RBSC/BSA/Engraving/bsa_engraving.bmp

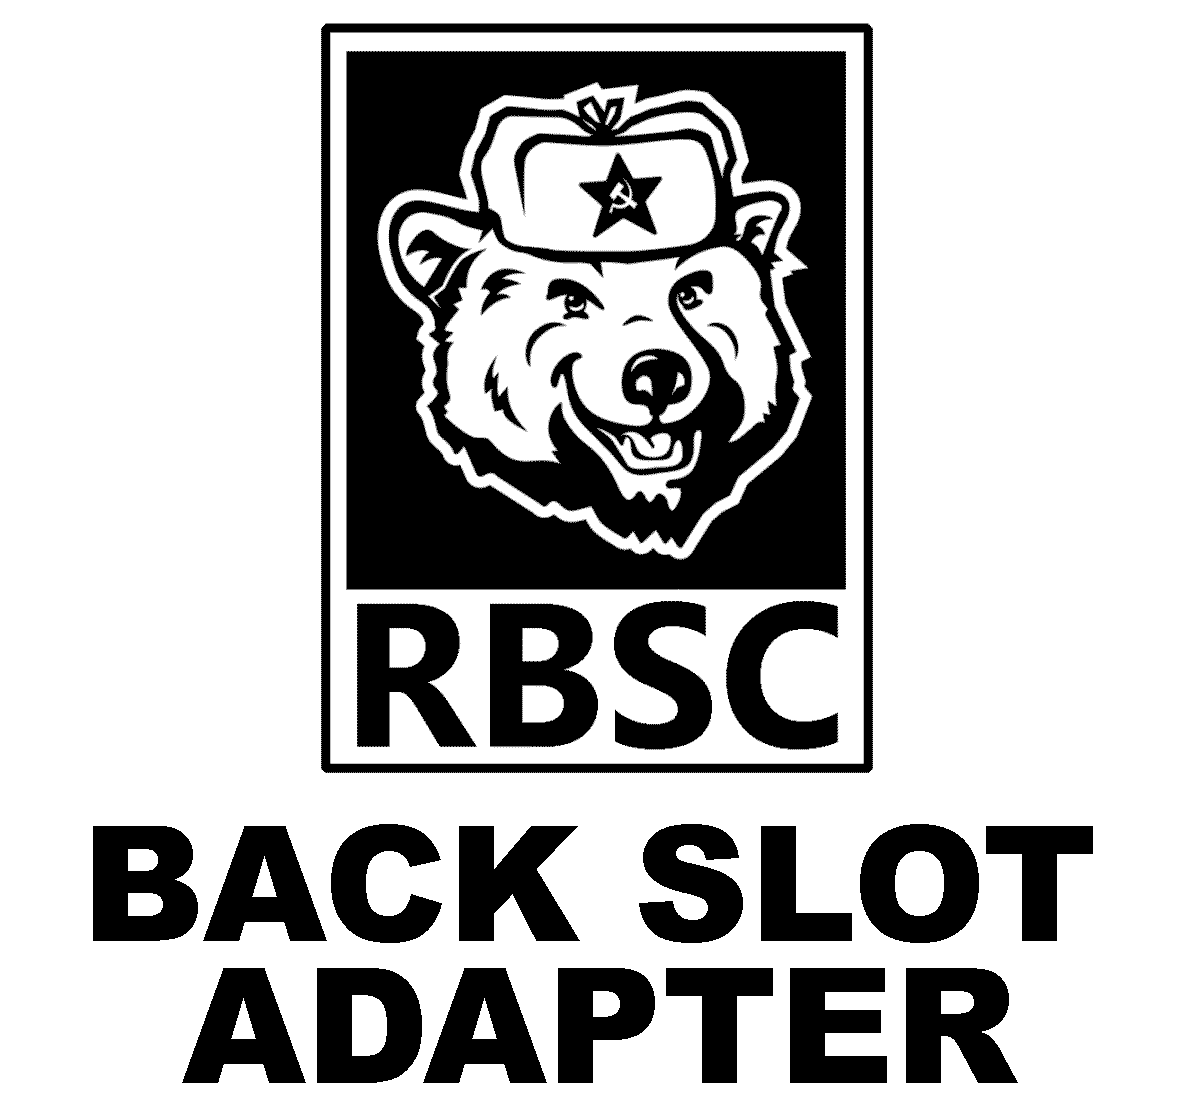
Engraving/bsa_engraving.bmp
