RBSC/BSA/Pics/board.jpg

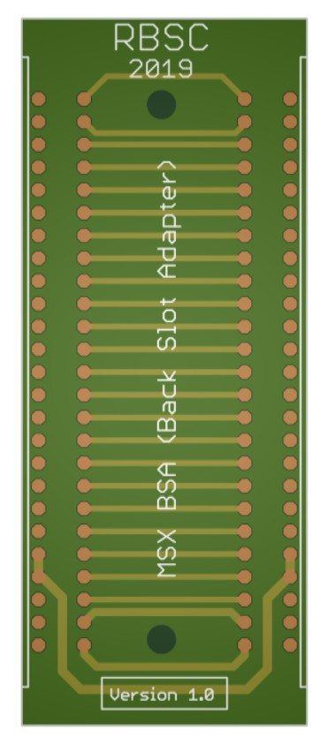
Pics/board.jpg
