RBSC/BSA/Pics/in1.jpg

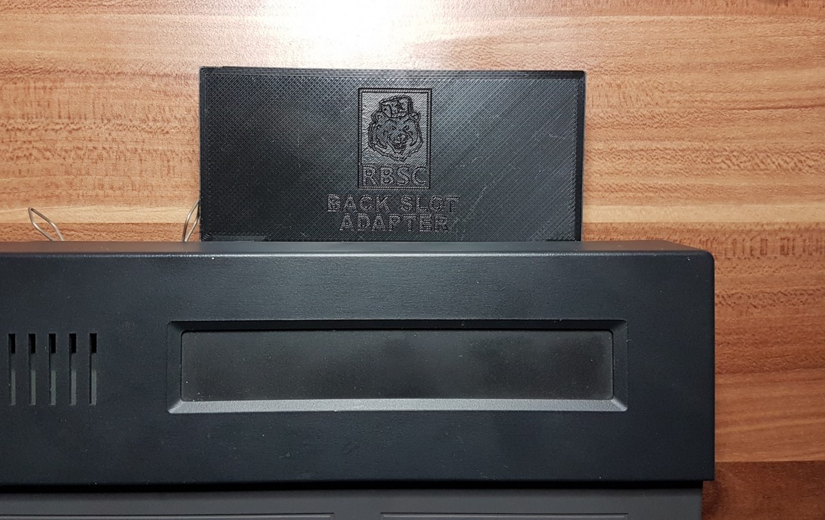
Pics/in1.jpg
