RBSC/BSA/Pics/ready.jpg

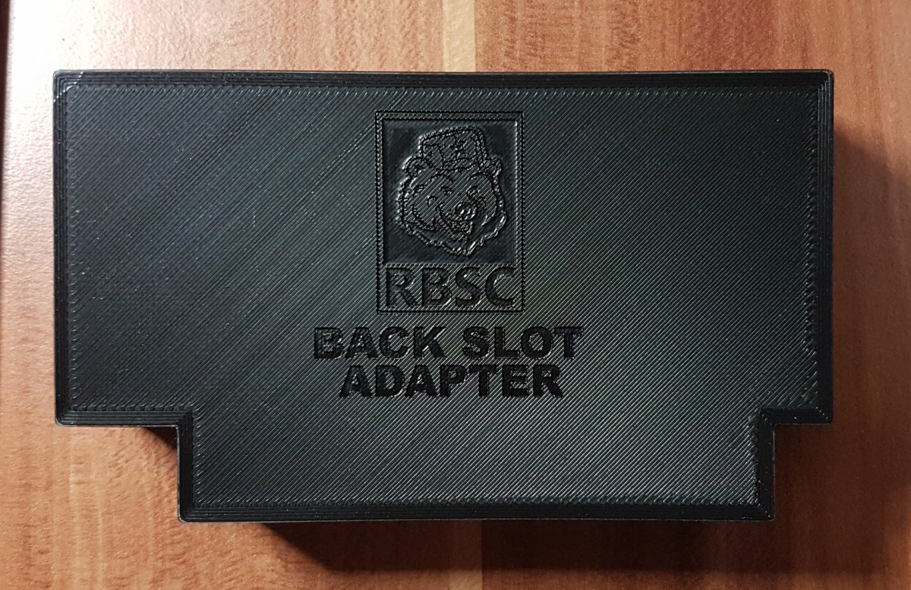
Pics/ready.jpg
