RBSC/BSA/Pics/slot.jpg

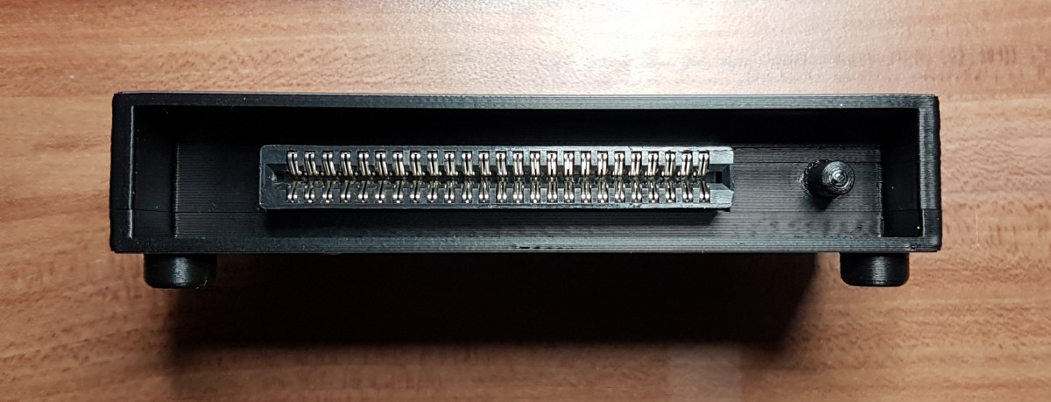
Pics/slot.jpg
