RBSC/BSA/Board/BackSlotAdapter.sch

## EAGLE design Board/BackSlotAdapter.sch (2019-07-26)

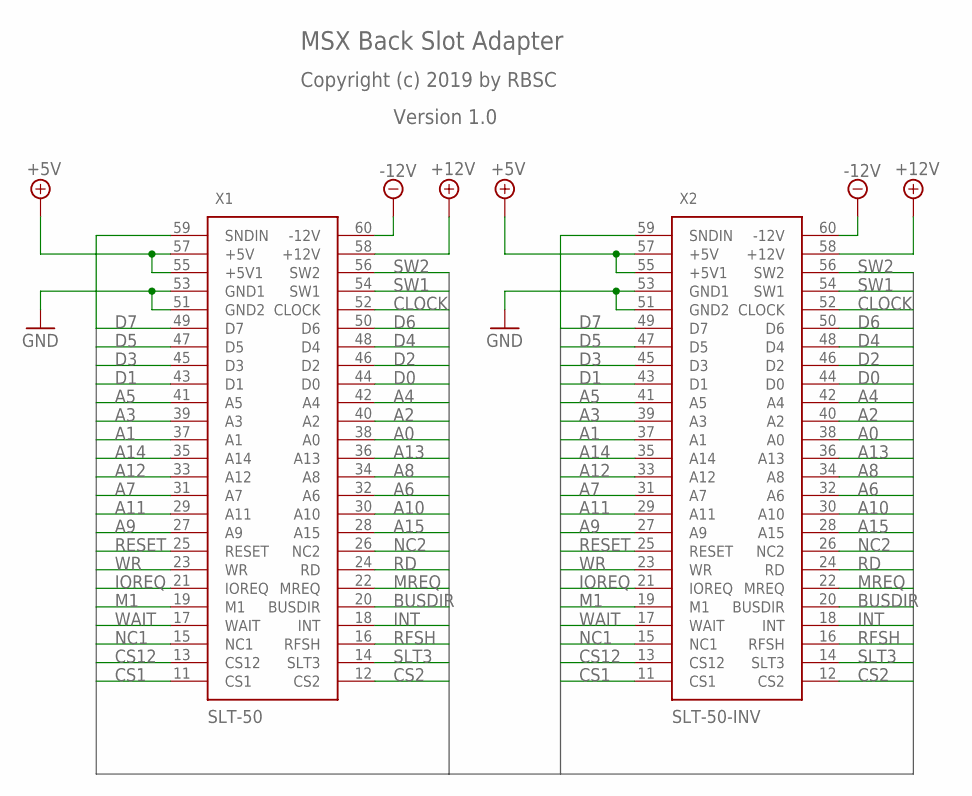
[picture p16: schematic BackSlotAdapter.sch]

Parts:
X1: SLT-50
X2: SLT-50-INV

Connections:
+5V: X1.55 (+5V1), X1.57 (+5V), X2.55 (+5V1), X2.57 (+5V)
+12V: X1.58 (+12V), X2.58 (+12V)
-12V: X1.60 (-12V), X2.60 (-12V)
A0: X1.38 (A0), X2.38 (A0)
A1: X1.37 (A1), X2.37 (A1)
A2: X1.40 (A2), X2.40 (A2)
A3: X1.39 (A3), X2.39 (A3)
A4: X1.42 (A4), X2.42 (A4)
A5: X1.41 (A5), X2.41 (A5)
A6: X1.32 (A6), X2.32 (A6)
A7: X1.31 (A7), X2.31 (A7)
A8: X1.34 (A8), X2.34 (A8)
A9: X1.27 (A9), X2.27 (A9)
A10: X1.30 (A10), X2.30 (A10)
A11: X1.29 (A11), X2.29 (A11)
A12: X1.33 (A12), X2.33 (A12)
A13: X1.36 (A13), X2.36 (A13)
A14: X1.35 (A14), X2.35 (A14)
A15: X1.28 (A15), X2.28 (A15)
BUSDIR: X1.20 (BUSDIR), X2.20 (BUSDIR)
CLOCK: X1.52 (CLOCK), X2.52 (CLOCK)
CS1: X1.11 (CS1), X2.11 (CS1)
CS2: X1.12 (CS2), X2.12 (CS2)
CS12: X1.13 (CS12), X2.13 (CS12)
D0: X1.44 (D0), X2.44 (D0)
D1: X1.43 (D1), X2.43 (D1)
D2: X1.46 (D2), X2.46 (D2)
D3: X1.45 (D3), X2.45 (D3)
D4: X1.48 (D4), X2.48 (D4)
D5: X1.47 (D5), X2.47 (D5)
D6: X1.50 (D6), X2.50 (D6)
D7: X1.49 (D7), X2.49 (D7)
GND: X1.51 (GND2), X1.53 (GND1), X2.51 (GND2), X2.53 (GND1)
INT: X1.18 (INT), X2.18 (INT)
IOREQ: X1.21 (IOREQ), X2.21 (IOREQ)
M1: X1.19 (M1), X2.19 (M1)
MREQ: X1.22 (MREQ), X2.22 (MREQ)
NC1: X1.15 (NC1), X2.15 (NC1)
NC2: X1.26 (NC2), X2.26 (NC2)
RD: X1.24 (RD), X2.24 (RD)
RESET: X1.25 (RESET), X2.25 (RESET)
RFSH: X1.16 (RFSH), X2.16 (RFSH)
SLT3: X1.14 (SLT3), X2.14 (SLT3)
SNDIN: X1.59 (SNDIN), X2.59 (SNDIN)
SW1: X1.54 (SW1), X2.54 (SW1)
SW2: X1.56 (SW2), X2.56 (SW2)
WAIT: X1.17 (WAIT), X2.17 (WAIT)
WR: X1.23 (WR), X2.23 (WR)

Notes on the sheet:
MSX Back Slot Adapter
Copyright (c) 2019 by RBSC
Version 1.0
